amos42/pcb_monitor_osd_control/monitor_osd_control/images/pcb_image_02.png

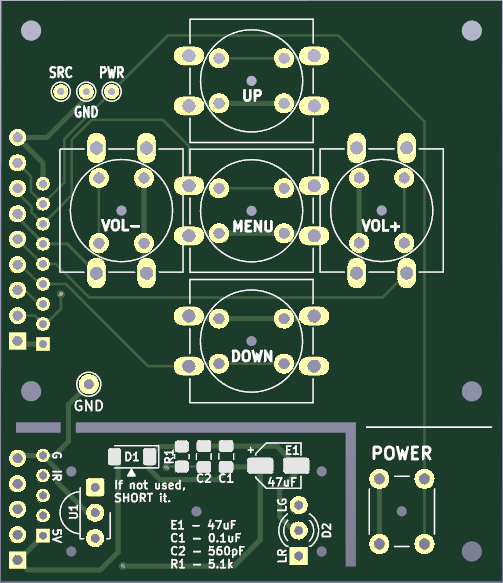
monitor_osd_control/images/pcb_image_02.png
